mahdiaredraki/A-Novel-3D-Printed-Device-for-Unconstrained-Grip-Force-Measurements/Experiment Data/Participant Datasets/Participant 1/Pinch Grasp/P1 - Pinch Grasp - Force Only - Easy - Trial 3.csv

Time | X_Position | Y_Position | Grip_Force | Vertical_Error | Grip_Force_Error
0 | 0.11 | 0.011758005 | 7.61289 | 0 | 0
0.0120000000000005 | 0.10925 | 0.01178433 | 7.61874 | 0 | 0
0.0241000000000007 | 0.1085 | 0.01180935 | 7.6243 | 0 | 0
0.0361000000000011 | 0.10775 | 0.01194615 | 7.6547 | 0 | 0
0.0485000000000007 | 0.107 | 0.012076155 | 7.68359 | 0 | 0
0.0600000000000005 | 0.10625 | 0.012437235 | 7.76383 | 0 | 0
0.0721000000000007 | 0.1055 | 0.012780225 | 7.84005 | 0 | 0
0.0841000000000012 | 0.10475 | 0.013106115 | 7.91247 | 0 | 0
0.0960000000000001 | 0.104 | 0.014008995 | 8.11311 | 0 | 0
0.108000000000001 | 0.10325 | 0.01486674 | 8.30372 | 0 | 0
0.120100000000001 | 0.1025 | 0.0156816 | 8.4848 | 0 | 0
0.132 | 0.10175 | 0.016640325 | 8.69785 | 0 | 0
0.144 | 0.101 | 0.01755108 | 8.90024 | 0 | 0
0.156000000000001 | 0.10025 | 0.018416295 | 9.09251 | 0 | 0
0.168100000000001 | 0.0995 | 0.01920582 | 9.26796 | 0 | 0
0.180200000000001 | 0.09875 | 0.01995588 | 9.43464 | 0 | 0
0.1921 | 0.098 | 0.02056824 | 9.57072 | 0 | 0
0.2041 | 0.09725 | 0.02115 | 9.7 | 0 | 0
0.216000000000001 | 0.0965 | 0.02170269 | 9.82282 | 0 | 0
0.228 | 0.09575 | 0.022204845 | 9.93441 | 0 | 0
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
