mahdiaredraki/A-Novel-3D-Printed-Device-for-Unconstrained-Grip-Force-Measurements/Experiment Data/Participant Datasets/Participant 1/Pinch Grasp/P1 - Pinch Grasp - Force Only - Easy - Trial 4.csv

Time | X_Position | Y_Position | Grip_Force | Vertical_Error | Grip_Force_Error
0 | 0.11 | 0.00930654 | 7.06812 | 0 | 0
0.0120499999999999 | 0.10925 | 0.00952839 | 7.11742 | 0 | 0
0.0240499999999999 | 0.1085 | 0.009745785 | 7.16573 | 0 | 0
0.0360300000000002 | 0.10775 | 0.009952335 | 7.21163 | 0 | 0
0.0480100000000001 | 0.107 | 0.01014858 | 7.25524 | 0 | 0
0.0600300000000002 | 0.10625 | 0.01036386 | 7.30308 | 0 | 0
0.0720399999999999 | 0.1055 | 0.010568385 | 7.34853 | 0 | 0
0.0840000000000001 | 0.10475 | 0.010762695 | 7.39171 | 0 | 0
0.0960900000000002 | 0.104 | 0.01097568 | 7.43904 | 0 | 0
0.10804 | 0.10325 | 0.011178 | 7.484 | 0 | 0
0.12001 | 0.1025 | 0.011383065 | 7.52957 | 0 | 0
0.13203 | 0.10175 | 0.011577915 | 7.57287 | 0 | 0
0.14403 | 0.101 | 0.011763 | 7.614 | 0 | 0
0.15603 | 0.10025 | 0.011911905 | 7.64709 | 0 | 0
0.16806 | 0.0995 | 0.012053385 | 7.67853 | 0 | 0
0.18001 | 0.09875 | 0.012231855 | 7.71819 | 0 | 0
0.19203 | 0.098 | 0.012401415 | 7.75587 | 0 | 0
0.20403 | 0.09725 | 0.01256247 | 7.79166 | 0 | 0
0.21602 | 0.0965 | 0.0128907 | 7.8646 | 0 | 0
0.22801 | 0.09575 | 0.013202505 | 7.93389 | 0 | 0
0.24005 | 0.095 | 0.01369476 | 8.04328 | 0 | 0
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
