mahdiaredraki/A-Novel-3D-Printed-Device-for-Unconstrained-Grip-Force-Measurements/Experiment Data/Participant Datasets/Participant 1/Pinch Grasp/P1 - Pinch Grasp - Force Only - Easy - Trial 5.csv

Time | X_Position | Y_Position | Grip_Force | Vertical_Error | Grip_Force_Error
0 | 0.11 | 0.017386065 | 8.86357 | 0 | 0
0.0110299999999999 | 0.10925 | 0.017283825 | 8.84085 | 0 | 0
0.0216899999999995 | 0.1085 | 0.01718676 | 8.81928 | 0 | 0
0.0317999999999996 | 0.10775 | 0.01709451 | 8.79878 | 0 | 0
0.04169 | 0.107 | 0.017010765 | 8.78017 | 0 | 0
0.0517300000000001 | 0.10625 | 0.01693116 | 8.76248 | 0 | 0
0.0617099999999997 | 0.1055 | 0.01685556 | 8.74568 | 0 | 0
0.0716999999999999 | 0.10475 | 0.01679787 | 8.73286 | 0 | 0
0.0831900000000001 | 0.104 | 0.01674306 | 8.72068 | 0 | 0
0.0952799999999998 | 0.10325 | 0.016690995 | 8.70911 | 0 | 0
0.10632 | 0.1025 | 0.016697745 | 8.71061 | 0 | 0
0.11732 | 0.10175 | 0.01670418 | 8.71204 | 0 | 0
0.12838 | 0.101 | 0.01685484 | 8.74552 | 0 | 0
0.14038 | 0.10025 | 0.01699794 | 8.77732 | 0 | 0
0.15224 | 0.0995 | 0.01713393 | 8.80754 | 0 | 0
0.16426 | 0.09875 | 0.01744479 | 8.87662 | 0 | 0
0.17625 | 0.098 | 0.01774008 | 8.94224 | 0 | 0
0.18828 | 0.09725 | 0.01802061 | 9.00458 | 0 | 0
0.20032 | 0.0965 | 0.01836504 | 9.08112 | 0 | 0
0.21228 | 0.09575 | 0.01869228 | 9.15384 | 0 | 0
0.22389 | 0.095 | 0.018965925 | 9.21465 | 0 | 0
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
