mahdiaredraki/A-Novel-3D-Printed-Device-for-Unconstrained-Grip-Force-Measurements/Experiment Data/Participant Datasets/Participant 1/Pinch Grasp/P1 - Pinch Grasp - Force Only - Hard - Trial 1.csv

Time | X_Position | Y_Position | Grip_Force | Vertical_Error | Grip_Force_Error
0 | 0.11 | 0.006668865 | 6.48197 | 0 | 0
0.011000000000001 | 0.10925 | 0.006622695 | 6.47171 | 0 | 0
0.0220000000000002 | 0.1085 | 0.006550875 | 6.45575 | 0 | 0
0.0329999999999995 | 0.10775 | 0.006482655 | 6.44059 | 0 | 0
0.0440000000000005 | 0.107 | 0.00641781 | 6.42618 | 0 | 0
0.0549999999999997 | 0.10625 | 0.00635301 | 6.41178 | 0 | 0
0.0660000000000007 | 0.1055 | 0.00629145 | 6.3981 | 0 | 0
0.077 | 0.10475 | 0.006232995 | 6.38511 | 0 | 0
0.088000000000001 | 0.104 | 0.00618336 | 6.37408 | 0 | 0
0.0990000000000002 | 0.10325 | 0.0061362 | 6.3636 | 0 | 0
0.109999999999999 | 0.1025 | 0.006091425 | 6.35365 | 0 | 0
0.121 | 0.10175 | 0.006080985 | 6.35133 | 0 | 0
0.132 | 0.101 | 0.00607104 | 6.34912 | 0 | 0
0.143000000000001 | 0.10025 | 0.006061635 | 6.34703 | 0 | 0
0.154 | 0.0995 | 0.00605952 | 6.34656 | 0 | 0
0.165000000000001 | 0.09875 | 0.00605754 | 6.34612 | 0 | 0
0.176 | 0.098 | 0.00605565 | 6.3457 | 0 | 0
0.186999999999999 | 0.09725 | 0.00611343 | 6.35854 | 0 | 0
0.1982 | 0.0965 | 0.006168285 | 6.37073 | 0 | 0
0.210000000000001 | 0.09575 | 0.006220395 | 6.38231 | 0 | 0
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
